ice3x2/kc2/docs/spec/20.kc2-no-stabilizer-layout.md

# KC2 No-Stabilizer Split Layout

| Field | Value |
|---|---|
| Document Type | layout_spec |
| Product | KC2 |
| Scope | Physical keyboard layout |
| Status | decided |
| Date | 2026-08-20 |
| Parent Spec | `../spec.md` |
| Related Research | `../research/kc2-plateless-low-profile-stabilizer-removal-2026-06-04.md` |

## 1. Purpose

This document defines the KC2 physical layouts for the plateless low-profile no-stabilizer direction. The verified `kc2-x3` baseline remains a 77-key layout, while the active `kc2-x3-v2` target uses the fixed 70-key v5 layout selected from 1:1 visual previews and subsequent left-thumb/modifier refinement.

Both variants split or replace every historical `>=2U` key so that no stabilizer is required. Duplicate legends such as `LShift`/`LShift`, `Enter`/`Enter`, and `Space`/`Space` are intentional physical-key decisions. Nonstandard keycaps may be 3D printed for the intended Choc V2 or MX assembly.

## 2. Policy

- Both no-stabilizer layouts use no `>=2U` physical keys, and `1.75U` is the largest permitted key width.
- The verified `kc2-x3` target retains its existing 77-key row extents and joined geometry.
- The active `kc2-x3-v2` target uses 70 keys and may reduce its PCB outline and joined geometry under `CON-ARCH-006`; the old `3.6 mm` inner-edge margin and fixed H1-H9 support pattern are not V2 invariants.
- V2 joined placement uses a `19.85 mm` one-unit seam pitch and a `1.80 mm` nominal gap between the actual selected keycap envelopes in both Choc V2 and MX assembly modes, within the tolerance defined by `CON-ARCH-006`. Rows 0-3 use `18.05 mm` / `18.05 mm` caps and `8.025 mm` center-to-PCB-edge offsets on both sides. The bottom `1.75U Space` / `1U B` seam uses `32.3375 mm` / `18.05 mm` caps, a `26.99375 mm` center pitch, and `15.16875 mm` / `8.025 mm` center-to-PCB-edge offsets. Every row retains a `3.80 mm` nominal joined PCB gap, and the complete joined Edge.Cuts polygons retain at least `1.00 mm` exact Euclidean clearance.
- Joined placement and reduced bezel shall not violate copper-to-edge, socket, pad, routing, manufacturing, controller, antenna, USB, reset, or battery-lead clearances.
- The verified historical `kc2-x3` compact controller keeps its `CON-ARCH-002` no-carrier-power contract: `J_PWR1` is absent and carrier battery power nets are absent. This rule does not apply to the active V2 target.
- The active `kc2-x3-v2` target follows `CON-ARCH-007`: each half has a direct-solder `J_BAT1`, local `BAT+`, `NN_B+`, and `GND`, and one `SW_PWR1` that interrupts BAT+ only. Battery negative remains directly connected to local GND. Pre-attached insulated battery leads are soldered to `J_BAT1`; detachable A2501/JST connectors, bare pouch-tab soldering, and a lower-housing battery-body cavity are prohibited. `BAT_LEAD_SLOT1` is a copper-free strain-relief feature identified by the exact board text `BAT STRAIN RELIEF`.
- V2 top-side service centers are exact: `J_BAT1` left `(115.8125, 59.4000)` R180 and right `(94.3000, 59.4000)` R0; `SW_PWR1` left `(115.8125, 63.4500)` R0 and right `(94.3000, 63.4500)` R180; `SW_RST1` left `(126.0625, 63.4500)` R0 and right `(84.0500, 63.4500)` R180. From each USB-facing outer edge toward the antenna, the order is POWER then RESET.
- Firmware may map duplicate physical legends to identical or separate behaviors; the physical layout intentionally does not force that choice.

## 3. KLE-Style JSON

### 3.1 Verified kc2-x3 77-key baseline

```json
{
  "left": [
    ["~", "1", "2", "3", "4", "5", "6"],
    [{ "w": 1.5 }, "TAB", "Q", "W", "E", "R", "T"],
    [{ "w": 1.75 }, "Caps", "A", "S", "D", "F", "G"],
    [{ "w": 1.25 }, "LShift", "LShift", "Z", "X", "C", "V", "B"],
    [{ "w": 1.25 }, "Ctrl", { "w": 1.25 }, "Win", { "w": 1.25 }, "Alt", { "w": 1.25 }, "Fn", "Space", { "w": 1.25 }, "Space"]
  ],
  "right": [
    [{ "x": 0.5 }, "7", "8", "9", "0", "-", "=", "BSPC", { "w": 1.25 }, "BSPC", "Del"],
    ["Y", "U", "I", "O", "P", "[", "]", { "w": 1.75 }, "\\", "Home"],
    [{ "x": 0.25 }, "H", "J", "K", "L", ";", "'", "Enter", { "w": 1.5 }, "Enter", "PgUp"],
    [{ "x": 0.75 }, "N", "M", ",", ".", "/", "RShift", "Fn", "Up", "PgDn"],
    [{ "x": 0.75 }, "B", "Space", "Space", "RAlt", "Fn", "RCtrl", "Left", "Down", "Right"]
  ]
}
```

### 3.2 Fixed kc2-x3-v2 70-key v5 layout

```json
{
  "left": [
    ["~", "1", "2", "3", "4", "5", "6"],
    [{ "w": 1.5 }, "TAB", "Q", "W", "E", "R", "T"],
    [{ "w": 1.75 }, "Caps", "A", "S", "D", "F", "G"],
    ["LShift", { "w": 1.25 }, "LShift", "Z", "X", "C", "V", "B"],
    [{ "w": 1.25 }, "Ctrl", { "w": 1.25 }, "Fn", { "w": 1.25 }, "Alt", { "w": 1.75 }, "Space", { "w": 1.75 }, "Space"]
  ],
  "right": [
    [{ "x": 0.5 }, "7", "8", "9", "0", "-", "=", { "w": 1.25 }, "BSPC", "Del"],
    ["Y", "U", "I", "O", "P", "[", "]", { "w": 1.75 }, "\\"],
    [{ "x": 0.25 }, "H", "J", "K", "L", ";", "'", { "w": 1.5 }, "Enter", "Enter"],
    [{ "x": 0.75 }, "N", "M", ",", ".", "/", "RShift", "Up", "Fn"],
    [{ "x": 0.75 }, "B", { "w": 1.75 }, "Space", { "w": 1.25 }, "RAlt", "RCtrl", "Left", "Down", "Right"]
  ]
}
```

## 4. Key Counts and Row Widths

| Variant | Half | Keys | Row widths including row offsets |
|---|---|---:|---|
| `kc2-x3` | Left | 32 | `7U`, `6.5U`, `6.75U`, `7.25U`, `7.25U` |
| `kc2-x3` | Right | 45 | `9.75U`, `9.75U`, `9.75U`, `9.75U`, `9.75U` |
| `kc2-x3` | Total | 77 | Verified baseline preserved |
| `kc2-x3-v2` | Left | 31 | `7U`, `6.5U`, `6.75U`, `7.25U`, `7.25U` |
| `kc2-x3-v2` | Right | 39 | `8.75U`, `8.75U`, `8.75U`, `8.75U`, `8.75U` |
| `kc2-x3-v2` | Total | 70 | Fixed v5 layout |

## 5. Split Decisions

| V2 area | Fixed v5 decision | Rationale |
|---|---|---|
| Left `Shift` | outer `1U LShift` + inner `1.25U LShift` | Places the wider Shift target on the inner/right position while remaining stabilizer-free. |
| Left bottom modifiers | `1.25U Ctrl`, `1.25U Fn` in the former Win position, `1.25U Alt` | Removes the former standalone 1U Fn switch and keeps a physical Fn on the left. |
| Left `Space` | `1.75U Space` + `1.75U Space` | Splits the removed Fn's 1U width evenly across the two Space keys without exceeding the no-stabilizer 1.75U limit. |
| Left Win behavior | simultaneous `Alt` + `Fn` -> `Win/LGUI` | Retains Win as a chord without a standalone physical Win switch. |
| Right top row | `1.25U BSPC` + `1U Del` | Replaces the former duplicate Backspace and removes the old outer Del column. |
| Right `Enter` | inner primary `1.5U Enter` + outer `1U Enter` | Matches the user's more comfortable Choc V1 experience. |
| Right shift row | `1U RShift` + `1U Up` + `1U Fn` | Moves Fn to the right of Up and removes PgDn. |
| Right bottom row | `1U B`, `1.75U Space`, `1.25U RAlt`, `1U RCtrl`, `1U Left`, `1U Down`, `1U Right` | Enlarges the main right Space without a stabilizer and fills the `8.75U` row. |
| Removed V2 keys | `Home`, `PgUp`, `PgDn`, one former right `Space`, and the former bottom-row right `Fn` position | Reduces the right half from 45 to 39 keys; Fn is retained beside Up. |

## 6. Implementation Notes

- The verified `kc2-x3` generator and firmware remain 77-key artifacts under `CON-ARCH-005`; they must not be silently converted to the V2 layout.
- The `kc2-x3-v2` generator, firmware transform, routing, housing, and fabrication manifests shall use the exact 70-key v5 map under `CON-ARCH-004`.
- Neither variant may create stabilizer markers, stabilizer footprints, or stabilizer keepouts.
- Right-side matrix column assignment must be regenerated and reviewed for the 39-key V2 half; naive row-array deletion is insufficient.
- The ZMK matrix and keymap should explicitly distinguish duplicate physical keys with stable physical IDs even when legends match.
- V2 joined visual and mechanical renders shall prove the keycap pitch and gap, concealed non-controller PCB outline, and the permitted controller/service exceptions defined by `CON-ARCH-006`.
- PCB regeneration, routing, firmware generation, housing generation, and DRC must be rerun after the V2 layout change. `CON-ARCH-004`, `CON-ARCH-006`, `CON-ARCH-007`, `REL-ARCH-001`, X-series preflight, fabrication-output inspection, deflection testing, and physical coupon/first-article evidence remain required before any orderable V2 claim.
- Historical `kc2-x3` regeneration must continue to prove `J_PWR1` and carrier battery nets are absent under `CON-ARCH-002`; these checks must not be applied to V2.
- Active `kc2-x3-v2` regeneration must instead prove the exact `CON-ARCH-007` `J_BAT1`/`SW_PWR1`/`SW_RST1` centers, BAT+ -> IMMS common -> ON throw -> `NN_B+`/U1 RAW continuity, direct B-/GND continuity, NC pad isolation, RST-to-GND behavior, strain relief, and component/copper/antenna/housing clearances.
