ice3x2/kc2/docs/reports/smooth-central-seam-20260914/wall-sections.png

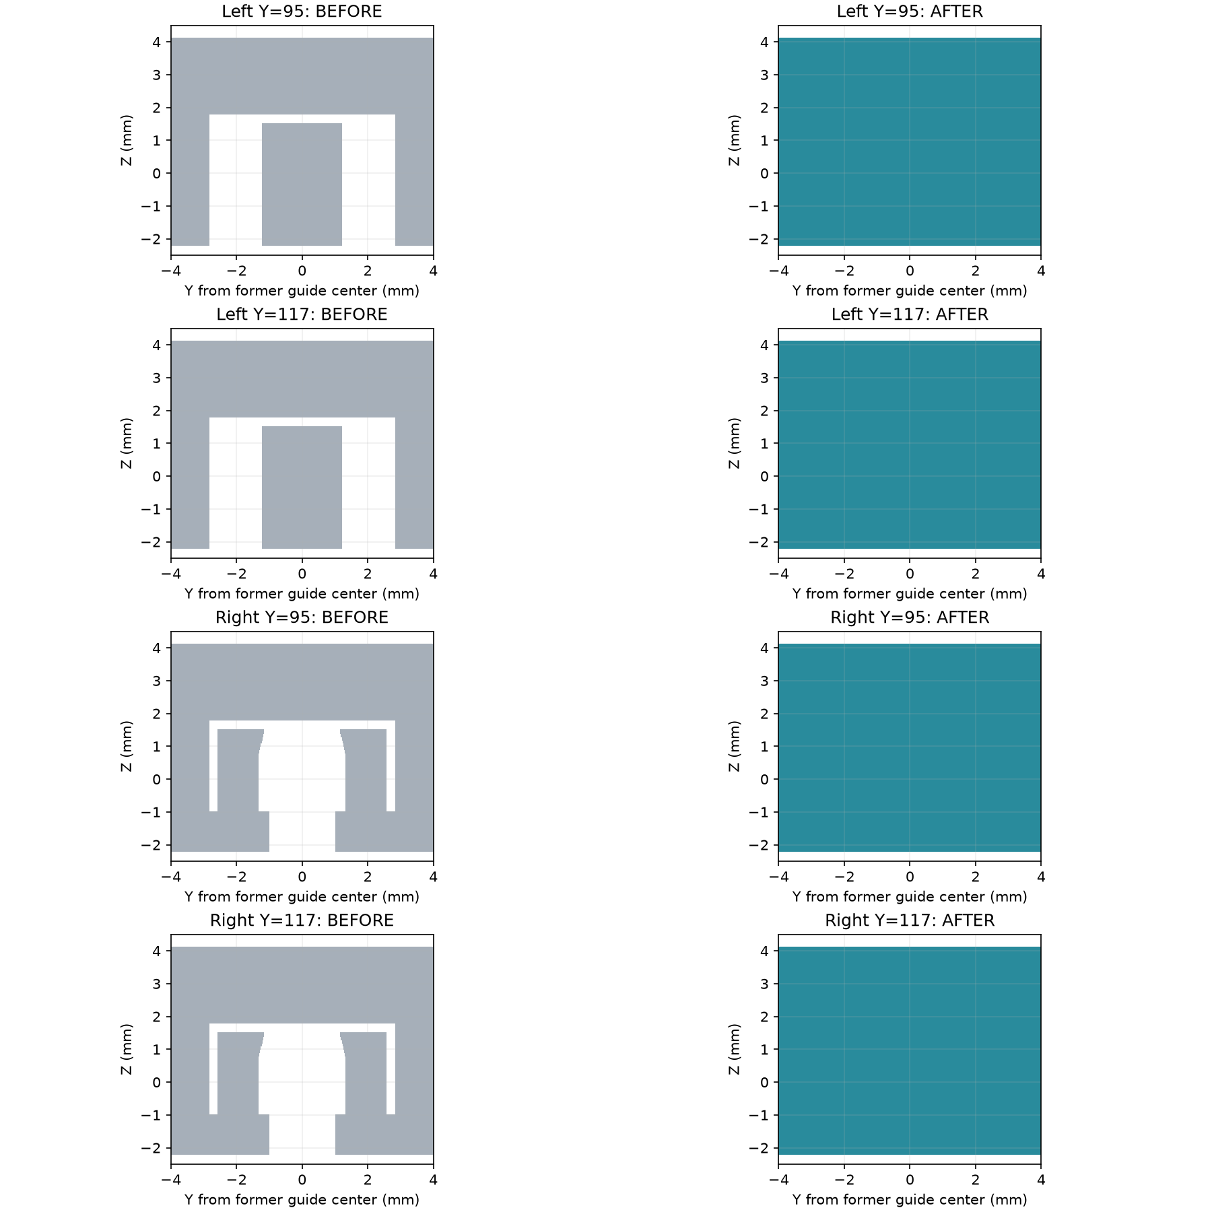
docs/reports/smooth-central-seam-20260914/wall-sections.png
