ice3x2/kc2/docs/reports/wrap-housings-20260920/left-sleeve-preview.png

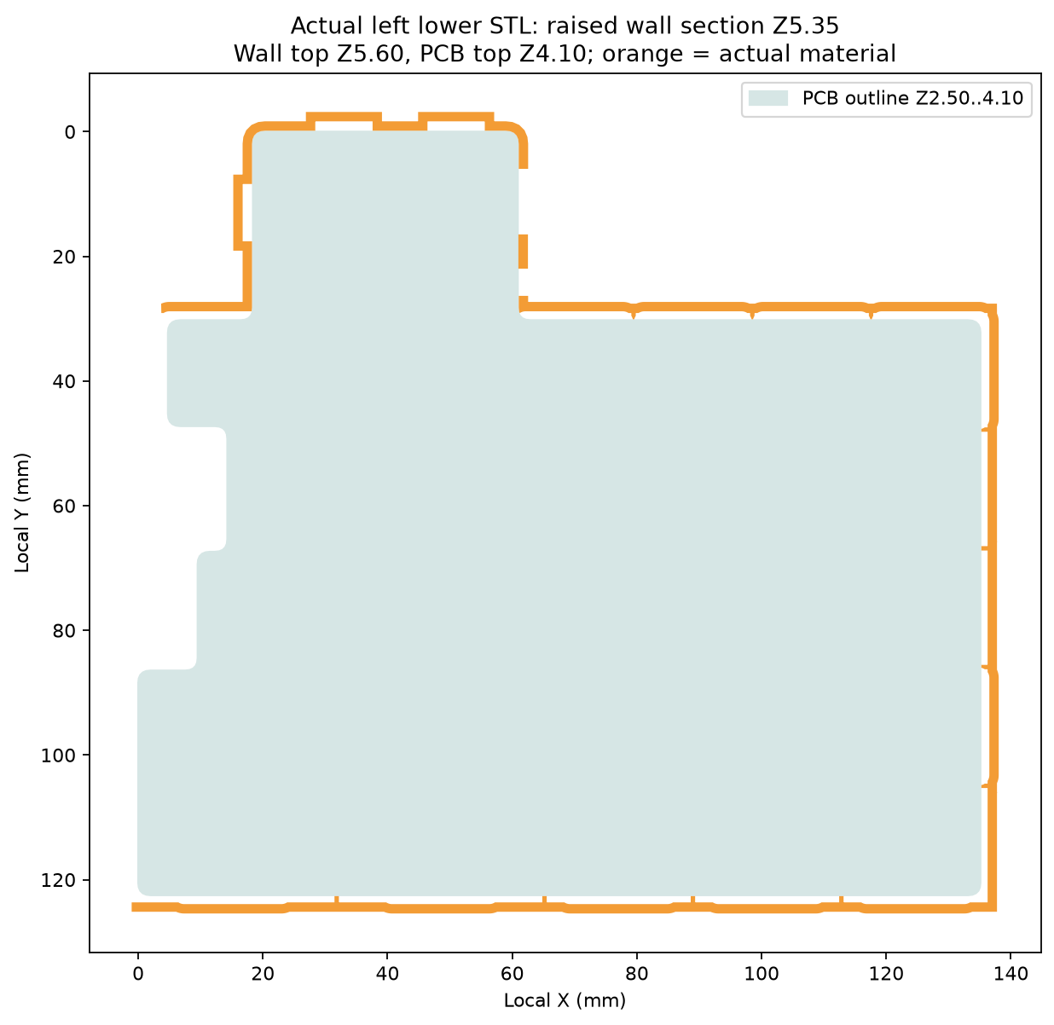
docs/reports/wrap-housings-20260920/left-sleeve-preview.png
