ice3x2/kc2/hardware/kicad/draft/hotswap/renders/kc2_left-hotswap_top.png

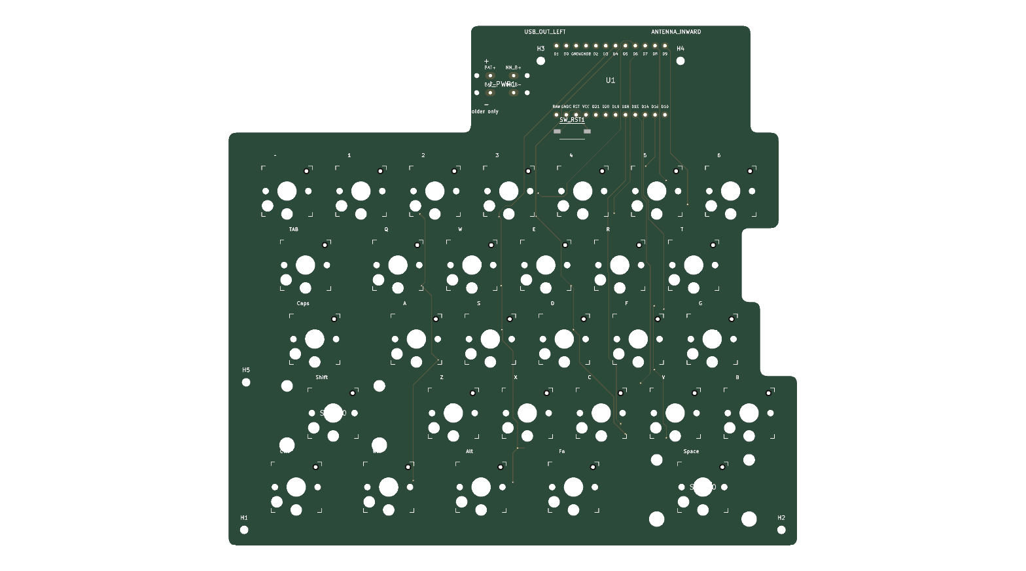
hardware/kicad/draft/hotswap/renders/kc2_left-hotswap_top.png
