ice3x2/kc2/hardware/kicad/fabrication_review/mx-visual-20260906/left-mechanical-1to1-preview.png

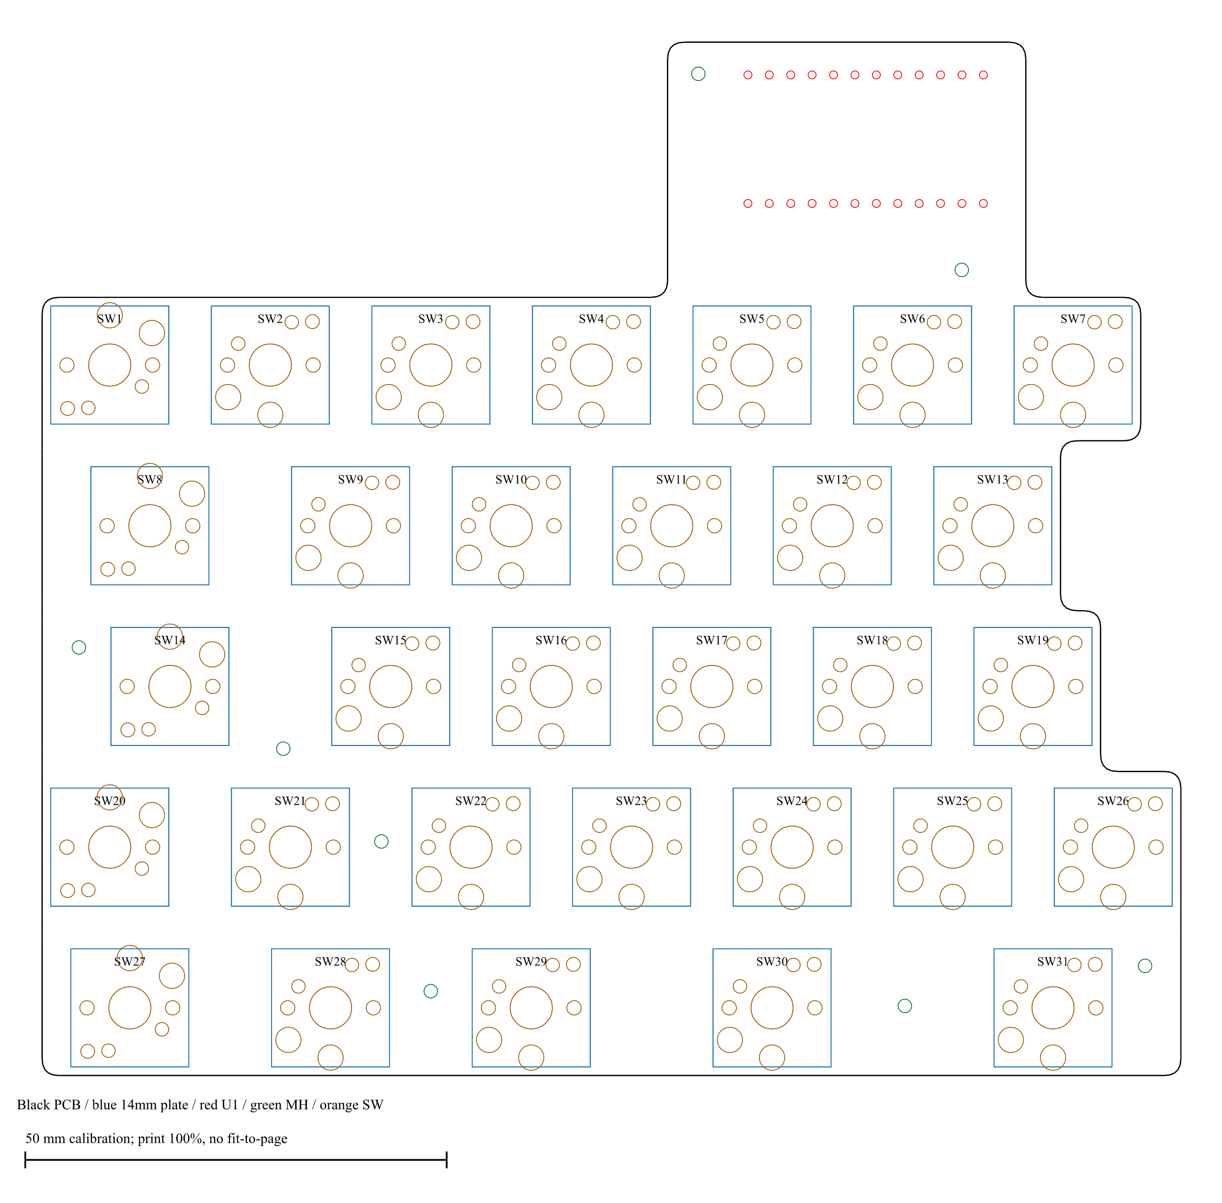
hardware/kicad/fabrication_review/mx-visual-20260906/left-mechanical-1to1-preview.png
