ice3x2/kc2/hardware/kicad/renders/kc2_join_seam_zoom.png

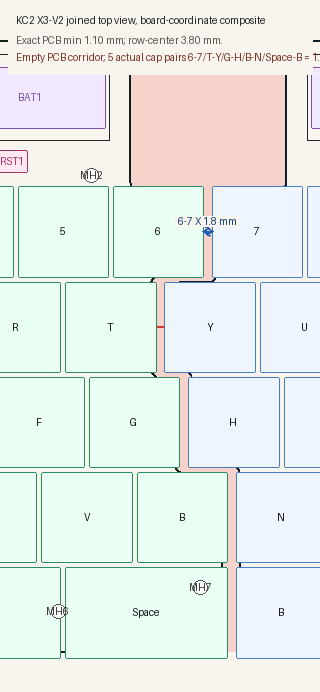
hardware/kicad/renders/kc2_join_seam_zoom.png
