ice3x2/kc2/hardware/kicad/renders/kc2_left_bottom.png

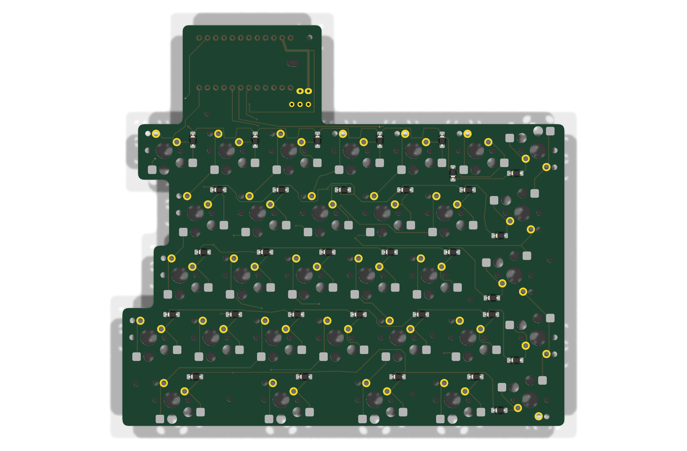
hardware/kicad/renders/kc2_left_bottom.png
