ice3x2/kc2/hardware/kicad/renders/kc2_right_bottom.png

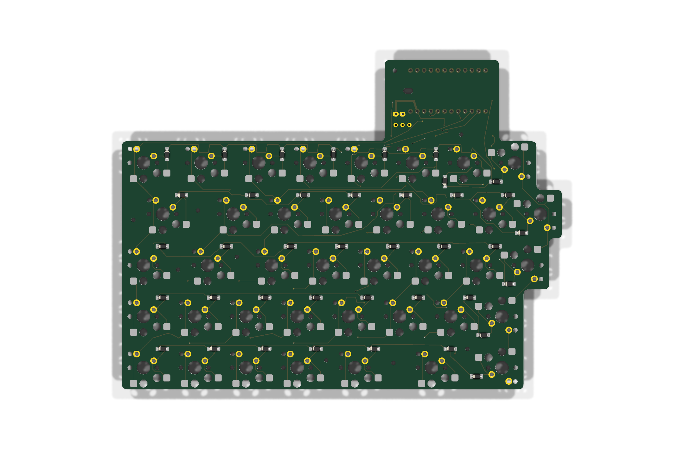
hardware/kicad/renders/kc2_right_bottom.png
