ice3x2/kc2/hardware/kicad/renders/kc2_right_top.png

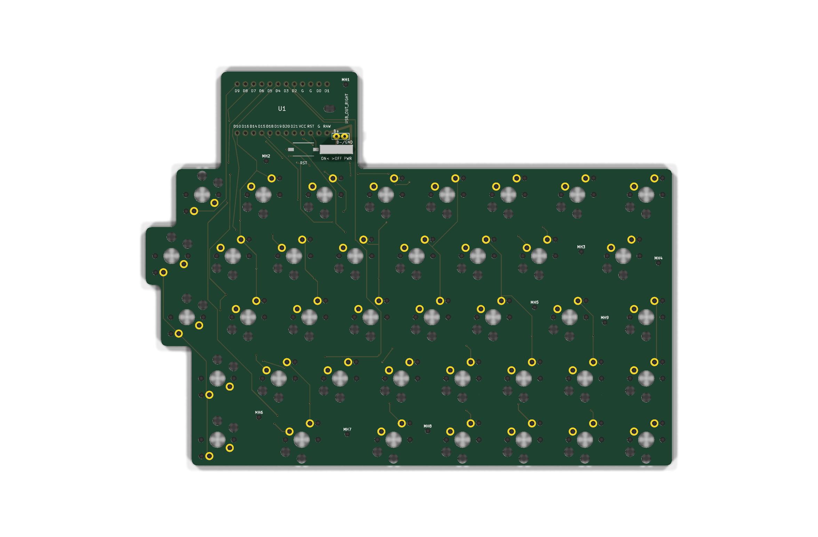
hardware/kicad/renders/kc2_right_top.png
