ice3x2/kc2/tmp_nw3/1322056_2.jpg

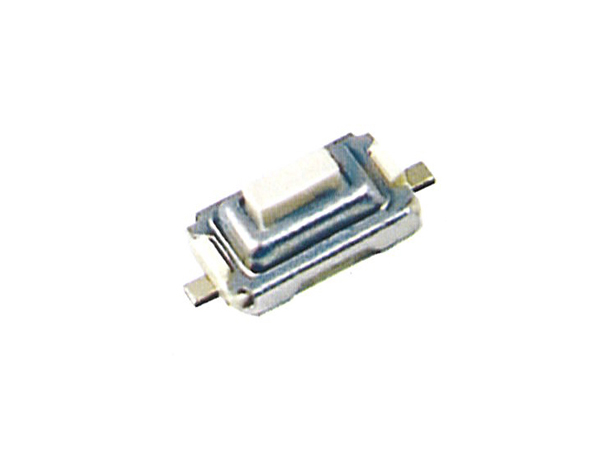
tmp_nw3/1322056_2.jpg
