ice3x2/kc2/hardware/kicad/fabrication/pcba_quote/kc2_left_jlcpcb_pcba_bom.csv

Comment | Designator | Footprint | LCSC Part #
Diodes Inc 1N4148W-13-F | D1,D2,D3,D4,D5,D6,D7,D8,D9,D10,D11,D12,D13,D14,D15,D16,D17,D18,D19,D20,D21,D22,D23,D24,D25,D26,D27,D28,D29,D30,D31 | SOD-123 | C112342
Kailh CPG135001S30 Choc hot-swap socket | SW1,SW2,SW3,SW4,SW5,SW6,SW7,SW8,SW9,SW10,SW11,SW12,SW13,SW14,SW15,SW16,SW17,SW18,SW19,SW20,SW21,SW22,SW23,SW24,SW25,SW26,SW27,SW28,SW29,SW30,SW31 | Kailh CPG135001S30 | C5333465
