ice3x2/kc2/hardware/MODELS/백업/kc2_right_lower_housing - 복사본.stl

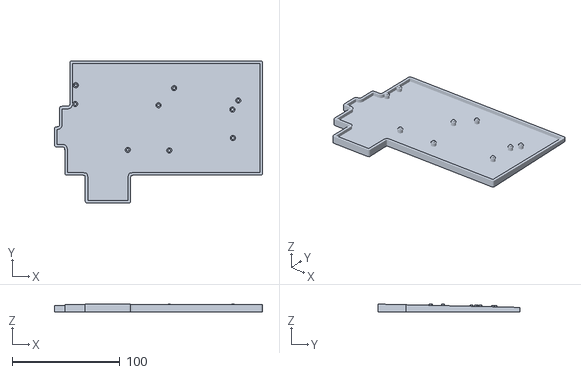
[picture p30: CAD file, 2026-06-15]
hardware/MODELS/백업/kc2_right_lower_housing - 복사본.stl
193.1 x 132.1 x 7.67
