ice3x2/kc2/docs/reports/reinforced-covers-20260913/native-check-left_lower_magnetic.step

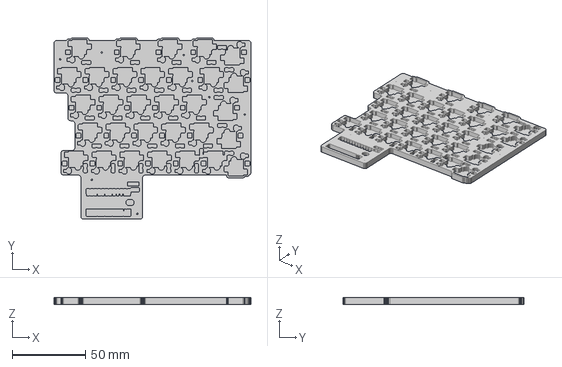
[picture p31: CAD file, 2026-09-12]
docs/reports/reinforced-covers-20260913/native-check-left_lower_magnetic.step
134.9 x 124.2 x 4.70 mm
