ice3x2/kc2/hardware/case/draft/x3-v2/kc2_right_x3_v2_lower_housing.step

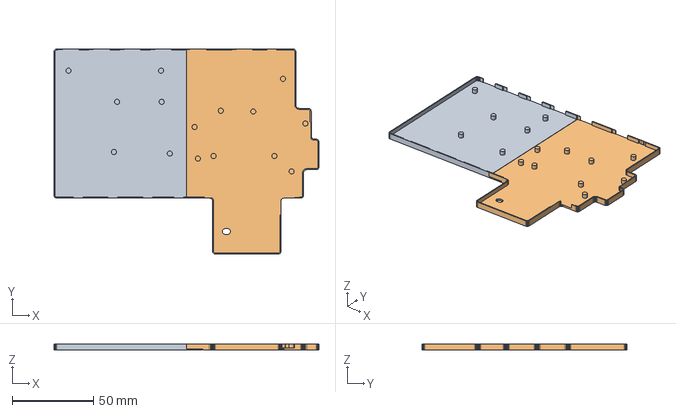
[picture p32: CAD file, 2026-08-20]
hardware/case/draft/x3-v2/kc2_right_x3_v2_lower_housing.step
163.5 x 126.6 x 3.90 mm
