ice3x2/kc2/hardware/case/kc2_right_lower_housing.step

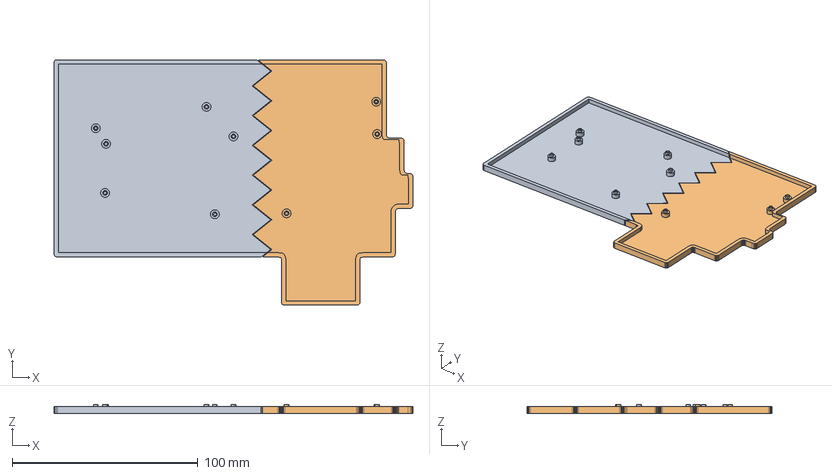
[picture p33: CAD file, 2026-08-03]
hardware/case/kc2_right_lower_housing.step
193.1 x 132.1 x 5.10 mm
