ice3x2/kc2/hardware/MODELS/adapters/kc2_mx_ring_cap_020.stl

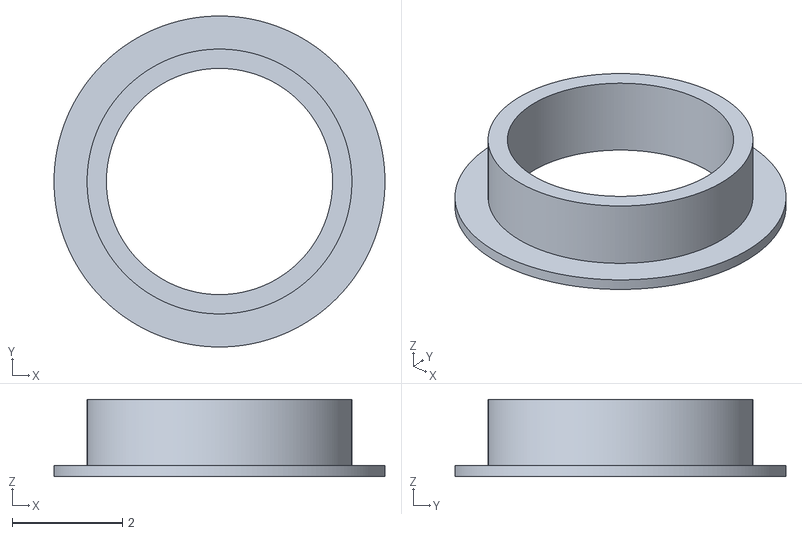
[picture p34: CAD file, 2026-09-06]
hardware/MODELS/adapters/kc2_mx_ring_cap_020.stl
6.00 x 6.00 x 1.40
