ice3x2/kc2/hardware/MODELS/kc2_right_lower_housing_part_b.stl

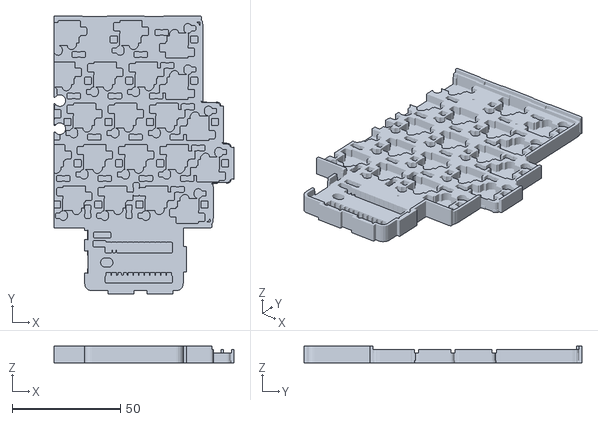
[picture p35: CAD file, 2026-09-21]
hardware/MODELS/kc2_right_lower_housing_part_b.stl
83.0 x 128.3 x 7.80
