ice3x2/kc2/hardware/MODELS/STL_FROM_FUSION_20260921/kc2_right_choc_v1_upper_housing_part_b.stl

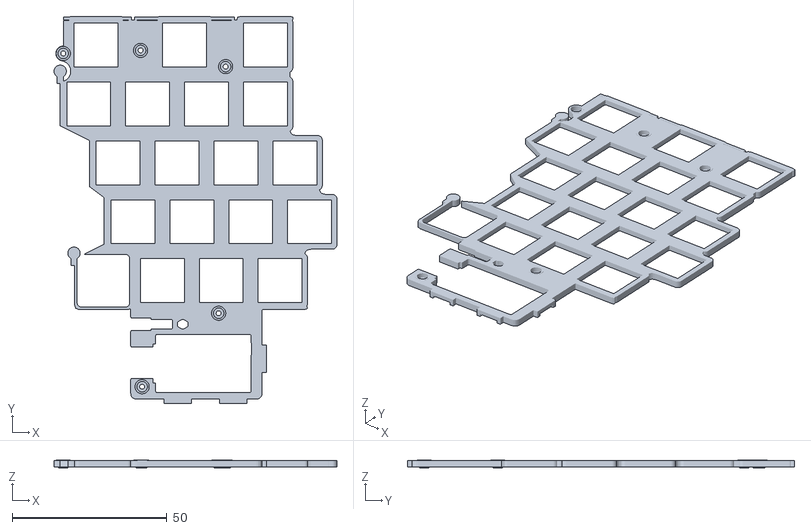
[picture p36: CAD file, 2026-09-21]
hardware/MODELS/STL_FROM_FUSION_20260921/kc2_right_choc_v1_upper_housing_part_b.stl
91.5 x 125.3 x 2.50
