ice3x2/kc2/hardware/MODELS/백업/kc2_left_lower_housing - 복사본.stl

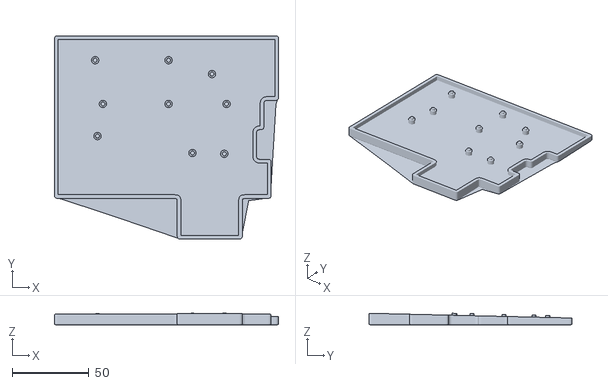
[picture p37: CAD file, 2026-06-15]
hardware/MODELS/백업/kc2_left_lower_housing - 복사본.stl
145.5 x 132.1 x 7.52
