ice3x2/kc2/docs/reports/registered-housing-fit-20260913/evidence/central/left-central-y95.step

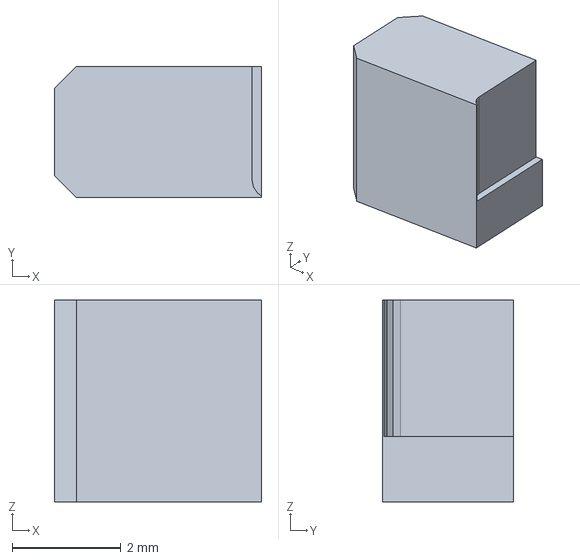
[picture p38: CAD file, 2026-09-14]
docs/reports/registered-housing-fit-20260913/evidence/central/left-central-y95.step
3.80 x 2.40 x 3.70 mm
