ice3x2/kc2/docs/reports/reinforced-covers-20260913/native-check-right_lower.step

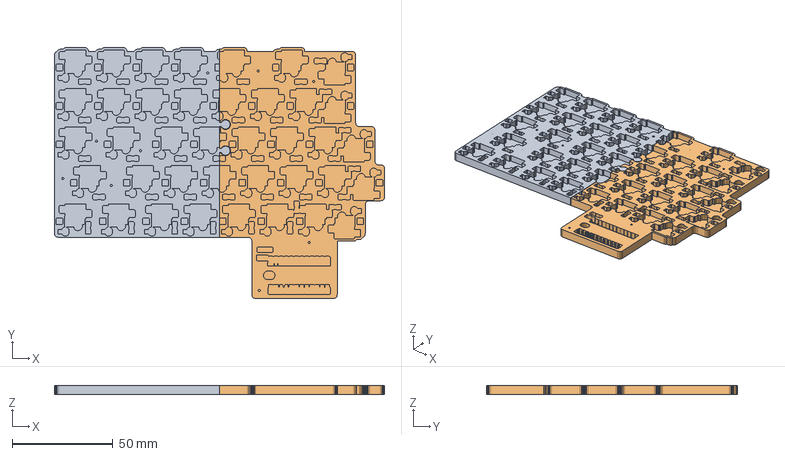
[picture p39: CAD file, 2026-09-12]
docs/reports/reinforced-covers-20260913/native-check-right_lower.step
163.5 x 124.2 x 4.70 mm
