ice3x2/kc2/hardware/MODELS/kc2_left_lower_housing.stl

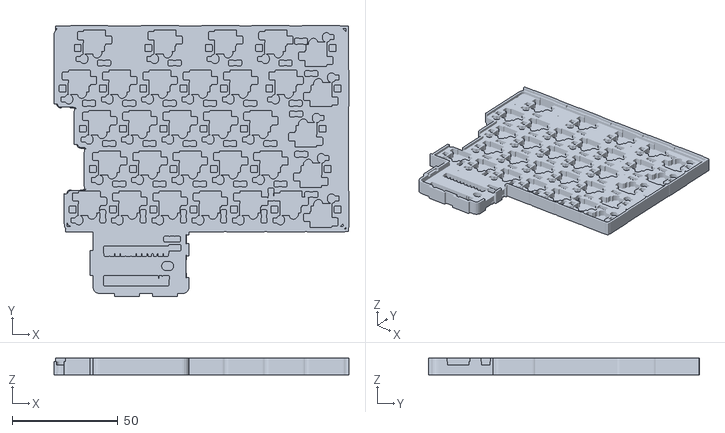
[picture p40: CAD file, 2026-09-21]
hardware/MODELS/kc2_left_lower_housing.stl
139.4 x 128.3 x 7.80
