ice3x2/kc2/hardware/MODELS/STL_FROM_FUSION_20260921/kc2_right_lower_housing_part_b_magnetic.stl

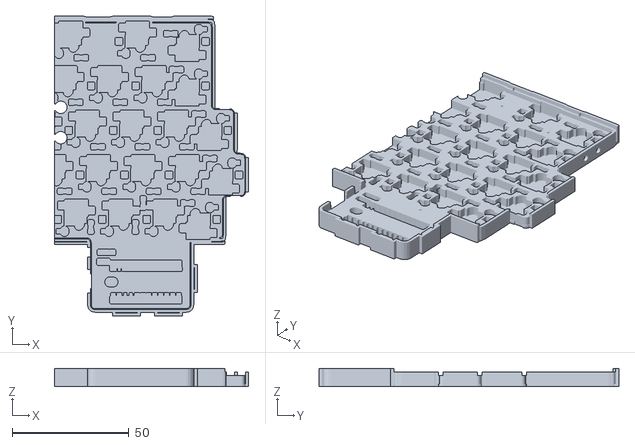
[picture p41: CAD file, 2026-09-21]
hardware/MODELS/STL_FROM_FUSION_20260921/kc2_right_lower_housing_part_b_magnetic.stl
83.0 x 128.3 x 7.80
