ice3x2/kc2/docs/reports/reinforced-covers-20260913/native-check-right_mx_upper.step

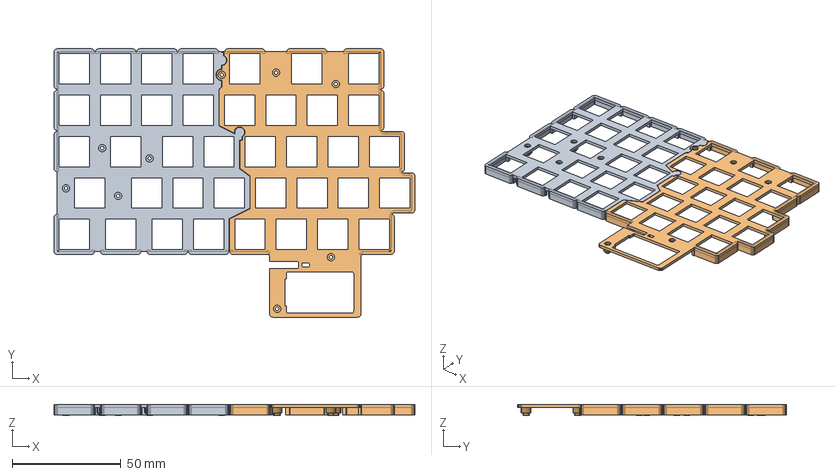
[picture p42: CAD file, 2026-09-12]
docs/reports/reinforced-covers-20260913/native-check-right_mx_upper.step
166.2 x 123.7 x 5.20 mm
