ice3x2/kc2/hardware/MODELS/kc2_right_deep_sea_upper_housing_part_a.stl

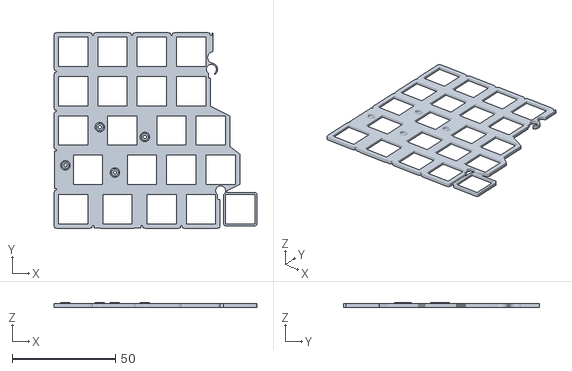
[picture p43: CAD file, 2026-09-21]
hardware/MODELS/kc2_right_deep_sea_upper_housing_part_a.stl
98.4 x 94.8 x 2.20
