ice3x2/kc2/hardware/MODELS/STL_FROM_FUSION_20260921/kc2_right_choc_v1_upper_housing_part_a.stl

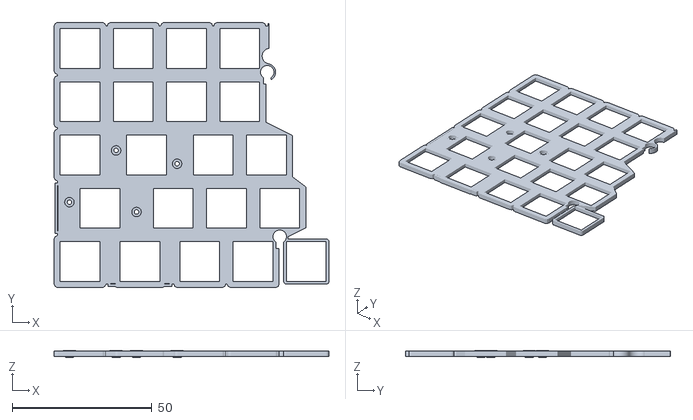
[picture p44: CAD file, 2026-09-21]
hardware/MODELS/STL_FROM_FUSION_20260921/kc2_right_choc_v1_upper_housing_part_a.stl
98.4 x 94.8 x 2.50
