ice3x2/kc2/hardware/MODELS/kc2_right_lower_housing_part_a.stl

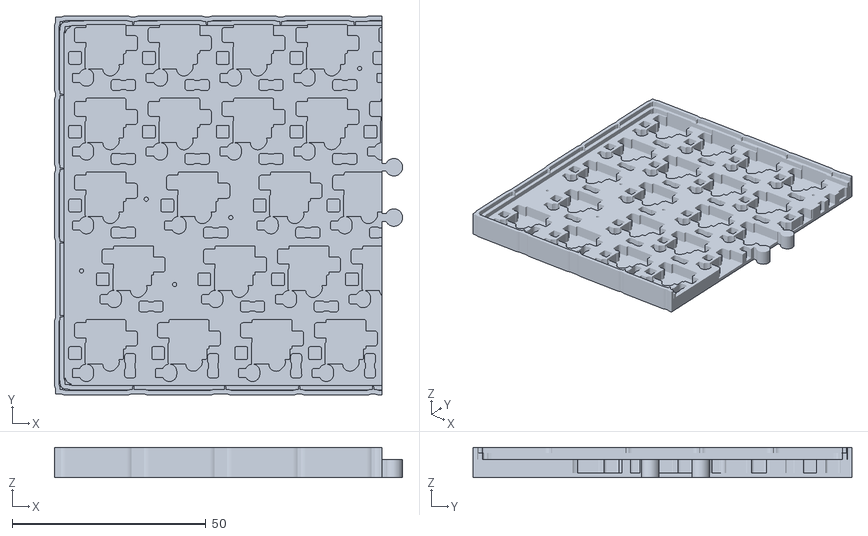
[picture p45: CAD file, 2026-09-21]
hardware/MODELS/kc2_right_lower_housing_part_a.stl
89.9 x 97.8 x 7.80
