ice3x2/kc2/hardware/MODELS/STL_FROM_FUSION_20260921/kc2_right_mx_upper_housing_part_b.stl

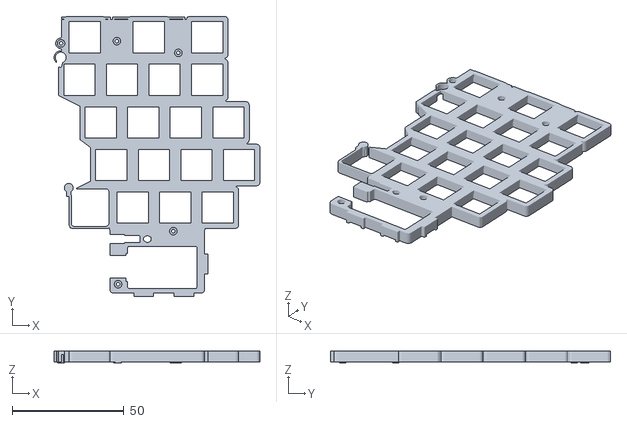
[picture p46: CAD file, 2026-09-21]
hardware/MODELS/STL_FROM_FUSION_20260921/kc2_right_mx_upper_housing_part_b.stl
92.1 x 125.3 x 5.20
