ice3x2/kc2/hardware/MODELS/kc2_right_deep_sea_upper_housing_part_b.stl

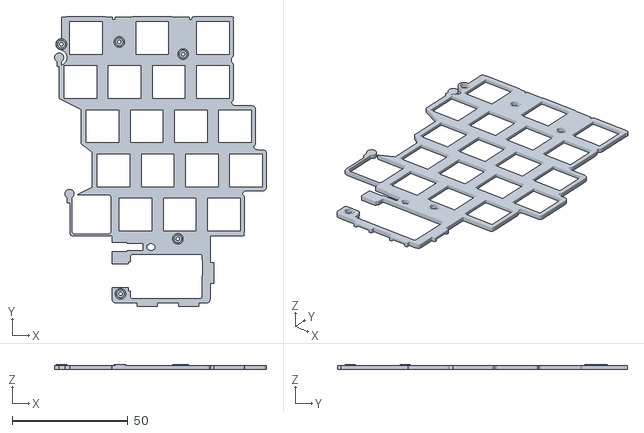
[picture p48: CAD file, 2026-09-21]
hardware/MODELS/kc2_right_deep_sea_upper_housing_part_b.stl
91.5 x 125.3 x 2.20
