ice3x2/kc2/hardware/MODELS/kc2_right_mx_upper_housing_part_a.stl

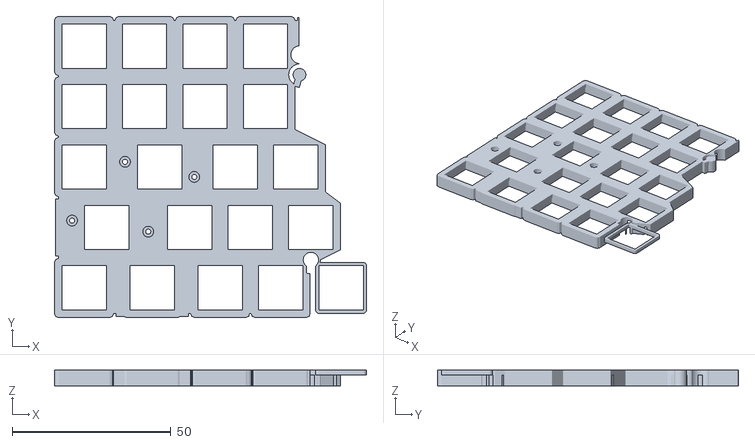
[picture p50: CAD file, 2026-09-21]
hardware/MODELS/kc2_right_mx_upper_housing_part_a.stl
98.3 x 94.8 x 4.90
