ice3x2/kc2/hardware/MODELS/STL_FROM_FUSION_20260921/kc2_right_lower_housing_part_a_magnetic.stl

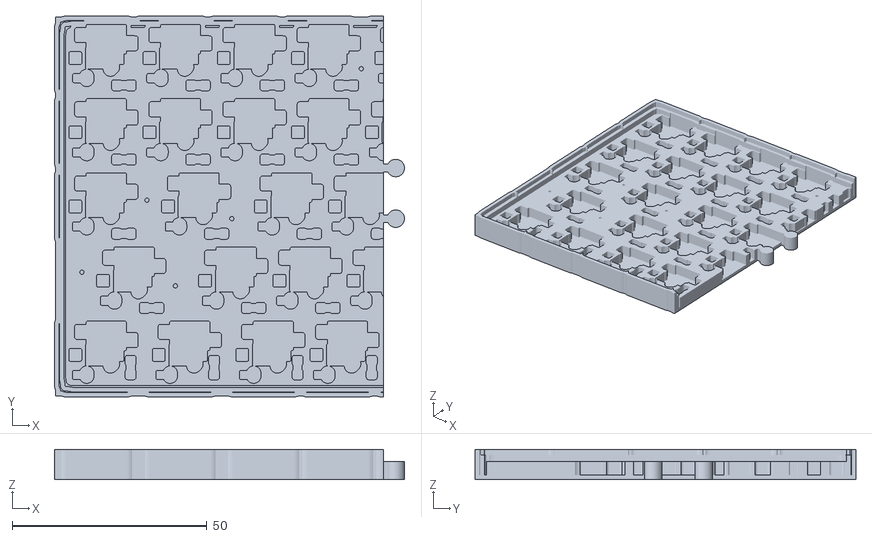
[picture p51: CAD file, 2026-09-21]
hardware/MODELS/STL_FROM_FUSION_20260921/kc2_right_lower_housing_part_a_magnetic.stl
89.9 x 97.8 x 7.80
