ice3x2/kc2/hardware/MODELS/kc2_left_deep_sea_upper_housing.stl

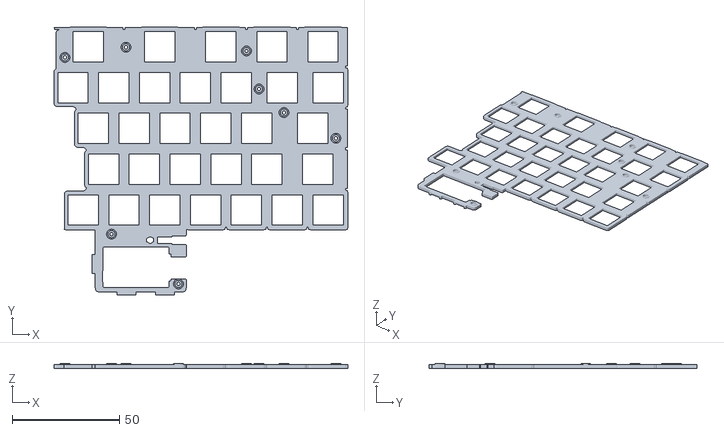
[picture p52: CAD file, 2026-09-21]
hardware/MODELS/kc2_left_deep_sea_upper_housing.stl
137.2 x 125.3 x 2.20
