ice3x2/kc2/hardware/MODELS/STL_FROM_FUSION_20260921/kc2_left_choc_v1_upper_housing.stl

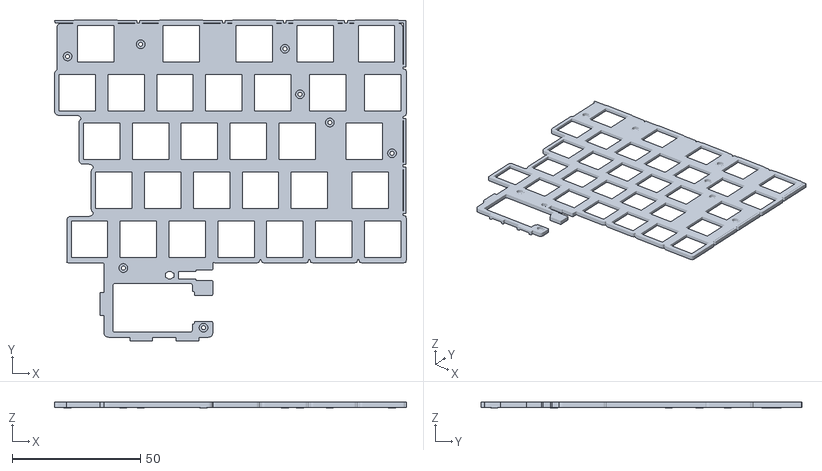
[picture p54: CAD file, 2026-09-21]
hardware/MODELS/STL_FROM_FUSION_20260921/kc2_left_choc_v1_upper_housing.stl
137.2 x 125.3 x 2.50
