ice3x2/kc2/hardware/MODELS/kc2_magnet_fit_coupon_magnetic.stl

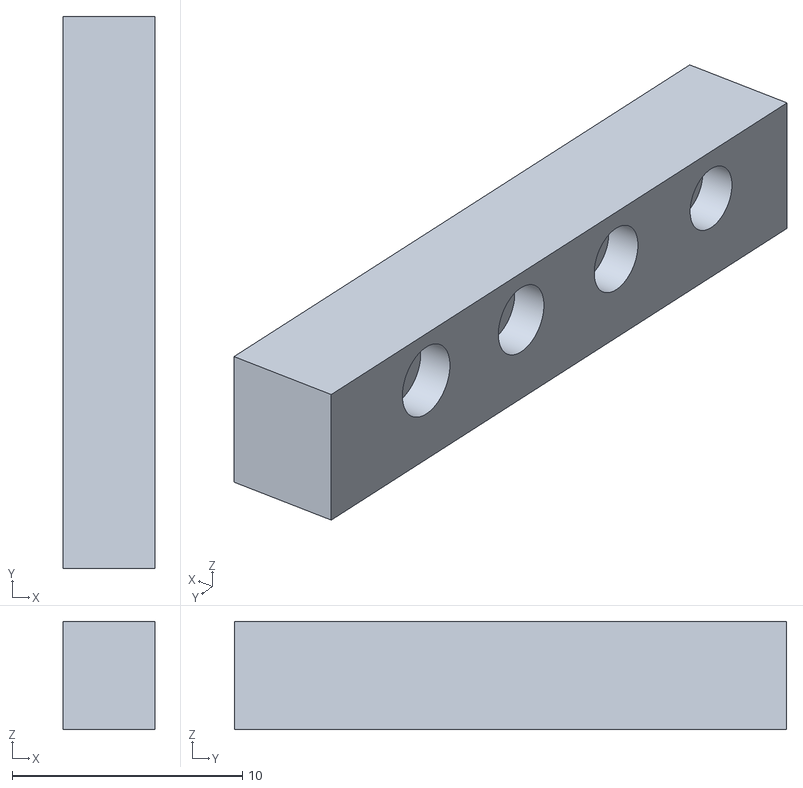
[picture p55: CAD file, 2026-09-07]
hardware/MODELS/kc2_magnet_fit_coupon_magnetic.stl
4.00 x 24.0 x 4.70
