ice3x2/kc2/hardware/MODELS/kc2_left_mx_upper_housing.step

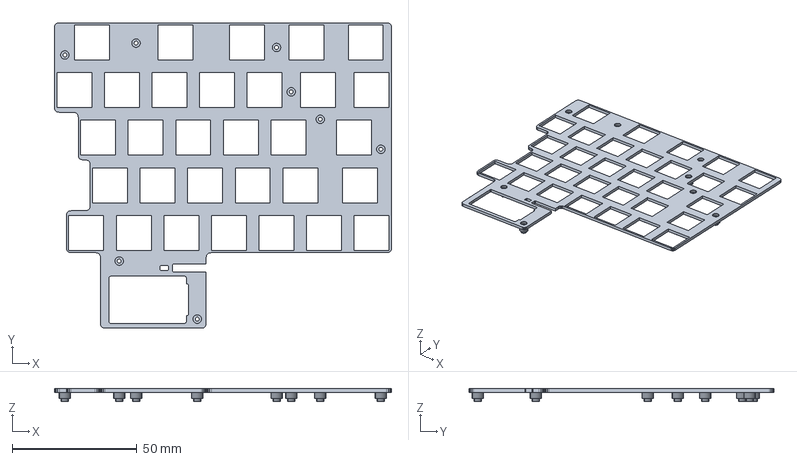
[picture p56: CAD file, 2026-09-07]
hardware/MODELS/kc2_left_mx_upper_housing.step
134.9 x 122.3 x 5.20 mm
