ice3x2/kc2/hardware/kicad/fabrication_review/mx-receptacle-20260906/README.md

# Inspection outputs — NOT APPROVED FOR ORDER

Requirements: CON-ARCH-004 AC-3/AC-8/AC-10, CON-ARCH-006, CON-ARCH-007.

This directory is for unzipped Gerber/Excellon inspection of the revised
canonical MX-receptacle PCB pair. It is not a fabrication release package.
No upload, purchase or assembly approval is given. Do not use historical
`hardware/kicad/fabrication/` ZIPs for this revised assembly.

Selected assembly: two individual open-bottom hat receptacles per switch,
with the printed MX plate-lid. Socket nominal length 3.00 mm, barrel OD 1.45 mm,
flange OD 2.00 mm, flange thickness 0.20 mm. MX finished-PTH design is a trial
1.60 mm; tolerance/contact fit is unqualified. U1 pads are 1.80 x 2.40 mm oval
with 0.95 mm drill; MX pads are 2.50 x 3.20 mm oval with 1.60 mm trial drill.

The generated copper/mask/drill files require source-geometry comparison and
visual inspection. Physical fit, exact MX switch, controller/service assembly,
housing fastener/printing qualification and power/RF testing remain open.
Do not infer readiness from file existence, DRC success or this directory name.
