ice3x2/kc2/docs/reports/registered-housing-fit-20260913/PRINT-draft.md

# 위치맞춤 외벽 하우징 — 게시 전 인쇄 안내 초안

이 문서는 보존된 이전 초안이며 현재 인쇄 지침이 아닙니다. [최종 인쇄 안내](../../../hardware/MODELS/PRINT-registered-housings.md)를 사용하세요.

요구사항: `CON-ARCH-006`, `CON-ARCH-007`, `OPS-ARCH-006`.
아직 최종 인쇄 승인이 아닙니다. 실제 검증과 canonical 게시 완료 후 사용할 안내 초안입니다.

## 부품 선택

상판은 MX, Choc V1, Deep Sea Mini 중 실제 스위치에 맞는 한 종류만 선택합니다. 각 종류의 왼쪽 STL 한 개와 오른쪽 `part_a`, `part_b` STL 각 한 개를 인쇄합니다. 하판은 무자석 또는 파일명에 `magnetic`이 있는 자석형 중 한 종류를 선택하여 같은 방식으로 세 개를 인쇄합니다. 총 상판 세 개와 하판 세 개입니다. 새 상판과 새 하판을 함께 사용하고 구형 부품을 섞지 마세요.

최종 게시 위치는 `hardware/MODELS`입니다. `.step`과 `.f3d`는 확인·편집용이며 오른쪽은 두 솔리드를 포함합니다. 150 mm 프린터에서는 반드시 분할 STL을 사용하세요. PCB와 이미 주문한 거버는 변경하지 않습니다.

`deep_sea`는 저상형 Deep Sea Mini 가족 도면 기준이며 일반 높이 Deep Sea Box용이 아닙니다. 구매 갈축 로트와 도면의 동일성은 아직 확인되지 않았습니다. Choc V1의 기존 0.20 mm 테두리 링 조건과 어댑터 안내는 유지합니다.

## 외벽과 조립

PCB는 종전처럼 하판 받침 위에 올립니다. PCB 바닥 Z2.50, 윗면 Z4.10이며, 외벽에 PCB를 압입하는 구조가 아닙니다. 기존 강화 소켓 가림벽을 유지합니다. 새 일반 외벽 상단은 Z4.10이고 넓은 상판 밑면 Z4.40과 명목 0.30 mm 여유가 있습니다.

각측 세 곳의 위치맞춤 돌기는 Z5.00까지 올라가며 상판의 외측 개방 홈에 들어갑니다. 홈 천장은 Z5.20, 안쪽면·양끝 여유는 한쪽 0.25 mm입니다. 돌기가 나사를 조이기 전 위치를 잡아주지만 나사 체결을 대신하지 않습니다. 중앙에는 위치맞춤 홈을 두지 않습니다. 공간이 부족한 중앙 세 구간에서는 새 상승벽만 국소 생략하고 기존 소켓 가림을 남깁니다.

오른쪽 A/B는 XY 방향으로 강제로 밀어 끼우지 말고 서로 맞물리는 위치에 높이를 달리해 놓은 뒤 Z 방향으로 내려 조립합니다. 명목 분할 여유는 약 0.40 mm입니다. 상판 맞물림은 머리 Ø4.00/목 2.00 mm, 하판은 머리 Ø4.50/목 2.00 mm입니다. 이는 좌우 키보드를 붙이는 중앙 결합부와 다른 구조·공차입니다.

좌우 전체 키보드는 중앙의 안내 혀 두 곳을 맞춰 수평으로 접근시킵니다. 중앙은 잠금 장치가 아니라 분리 가능한 국소 접촉 구조입니다. 끝부분의 명목 접촉량 0.02 mm는 실제 끼움 힘을 보증하는 값이 아닙니다. 출력 편차에 따라 헐겁거나 빡빡할 수 있으므로 힘으로 밀어 넣지 마세요.

## 출력과 물리 확인

- 단위 mm, 배율 100%. 전체 축척을 줄이면 스위치와 나사 위치가 PCB와 달라집니다.
- 하판은 평평한 바닥을 아래로 놓습니다. 새 중앙 탄성부의 빈 공간은 의도된 공간이므로 인필이나 접착제로 메우지 마세요.
- 오른쪽 중앙 두 곳에는 길이 5.70 mm의 국소 브리지가 있습니다. 해당 브리지와 탄성부 주변의 실제 슬라이서 경로를 확인해야 합니다. 지지 없이 반드시 인쇄된다는 보증은 아닙니다.
- 상판은 넓은 판 윗면을 아래로 놓는 방향을 검토합니다. V1 나사 보스는 판보다 0.10 mm, Deep Sea 보스는 0.35 mm 높아 뒤집었을 때 판 밑에 얕은 공중 시작 영역이 생깁니다. 빌드플레이트 연결 서포트 등으로 첫 층부터 지지되는지 확인하세요.
- 명목 1.20 mm 가림벽에 실제 연속 경로가 충분히 생성되는지 확인합니다. CAD가 솔리드여도 슬라이서는 인필을 만들 수 있으므로 내부까지 꽉 채운 출력물이 목적이라면 100% 인필을 사용하고 실제 경로를 별도로 확인하세요.
- 첫 층 눌림, 실뭉침, 브리지 처짐은 결합을 막을 수 있습니다. 중앙 끼움·A/B·위치맞춤 홈과 자석 입구를 먼저 시험 출력하여 확인하는 것이 좋습니다. 디지털 검증만으로 재료 강도·마찰·피로·흡착력은 확정할 수 없습니다.

## 나사와 자석

MX는 명목 M1.4×7.50 mm, 저상형은 M1.4×5.00 mm입니다. 길이는 머리 아래부터 측정합니다. MX 나사를 저상형에 사용하지 마세요. 통과 홀 Ø1.60 mm, 머리 포켓 Ø3.40 mm이며 설계 머리 범위는 최대 Ø3.00×높이 1.20 mm입니다. 나사 힘으로 들뜸이나 휨을 눌러 맞추지 마세요.

자석형은 Ø2×두께 1 mm 원통 자석용 기존 Ø2.40×깊이 1.20 mm 홈을 유지합니다. 새 외벽에 동축 Ø2.40 mm 삽입 통로를 추가하므로 바깥 입구에서 홈 뒷면까지는 2.80 mm입니다. 이 값은 자석을 받는 기존 홈 자체의 깊이와 다릅니다. 자석은 새 외벽의 통로를 지나 원래 안쪽 블라인드 홈에 안착시켜야 하며, 새 바깥 통로에 고정하지 마세요. 좌우 자석 극성을 먼저 확인하고 실제 끼움·접착·흡착력은 출력 후 확인하세요. 무자석형에는 삽입 통로가 없습니다.

실리콘 발의 배치와 접착 검토는 사용자 지시에 따라 이번 작업에서 보류했습니다.

조립 후 PCB 받침 접촉, 스위치 완전 안착·클립, 전원/리셋/USB 접근, 모든 키캡의 완전 눌림과 나사 머리 간섭을 직접 확인해야 합니다. 실제 납땜 돌출, 배선, 구매 부품 편차, 체결 토크 및 RF는 별도 물리 확인 대상입니다.
