ice3x2/kc2/docs/reports/wrap-housings-20260920/assembly-section-left-mx.png

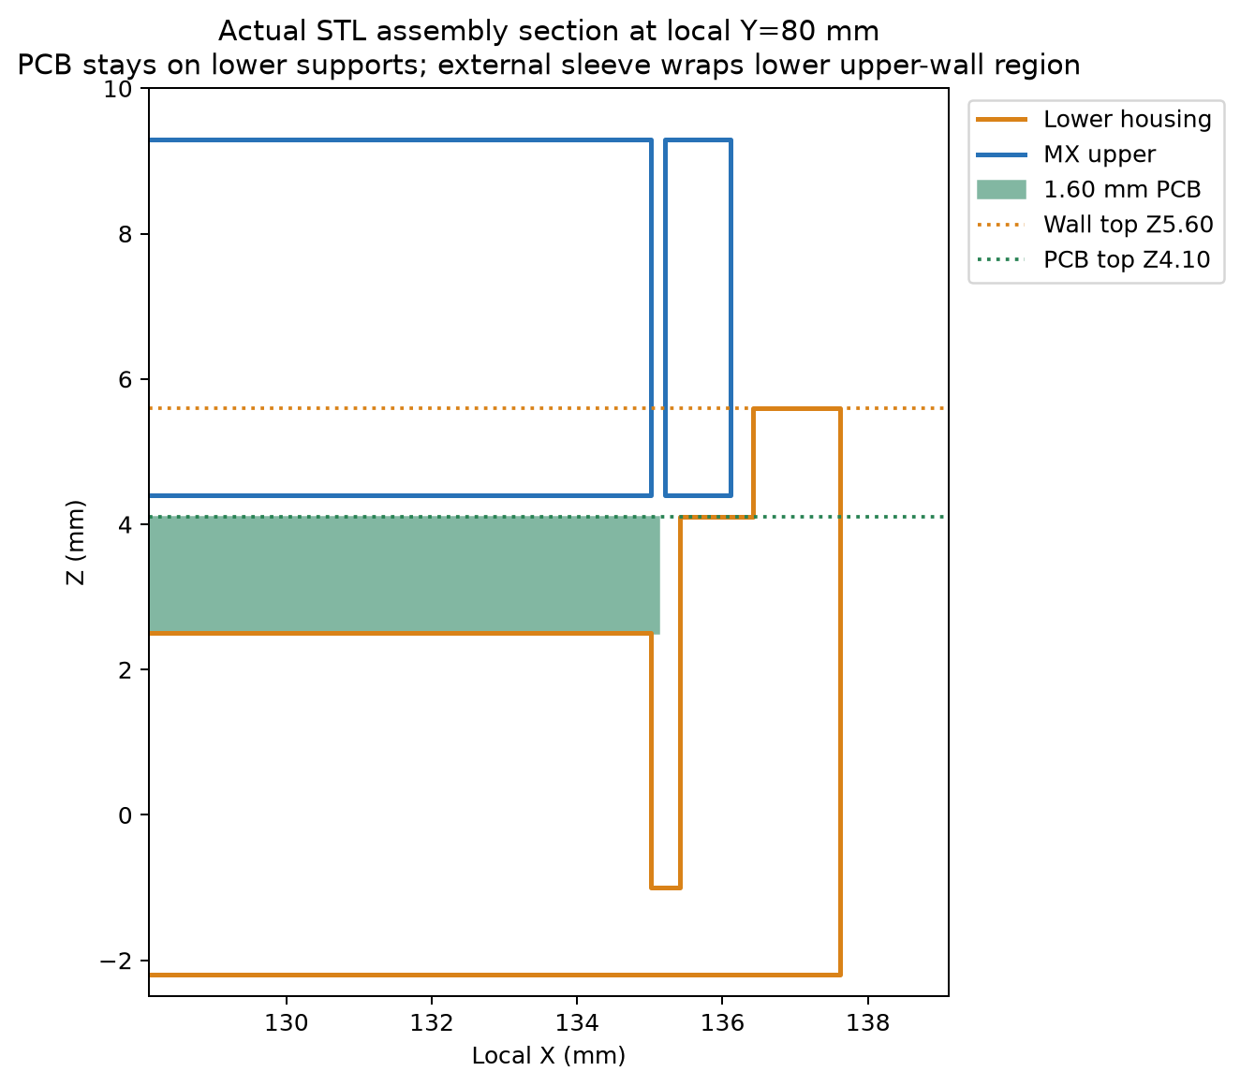
docs/reports/wrap-housings-20260920/assembly-section-left-mx.png
