ice3x2/kc2/hardware/kicad/draft/soldered/renders/kc2_left_top.png

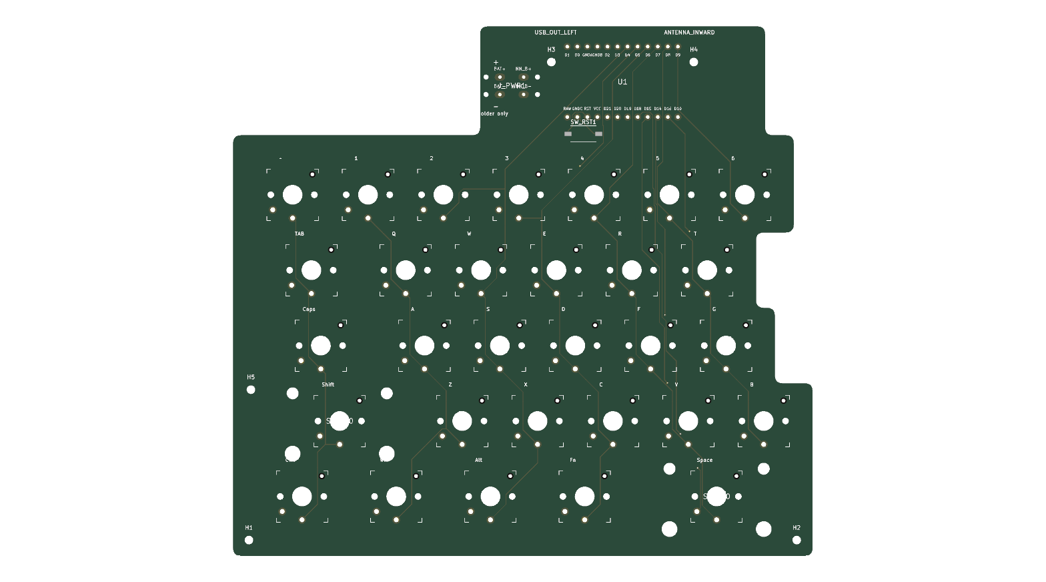
hardware/kicad/draft/soldered/renders/kc2_left_top.png
