ice3x2/kc2/hardware/kicad/fabrication_review/mx-visual-20260906/left-B_Cu-tile-0-0.png

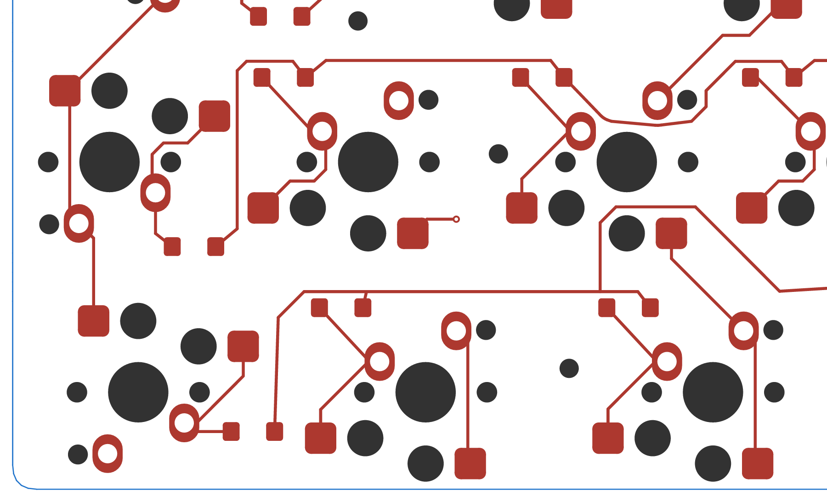
hardware/kicad/fabrication_review/mx-visual-20260906/left-B_Cu-tile-0-0.png
