ice3x2/kc2/hardware/kicad/fabrication_review/mx-visual-20260906/left-F_Mask-service.png

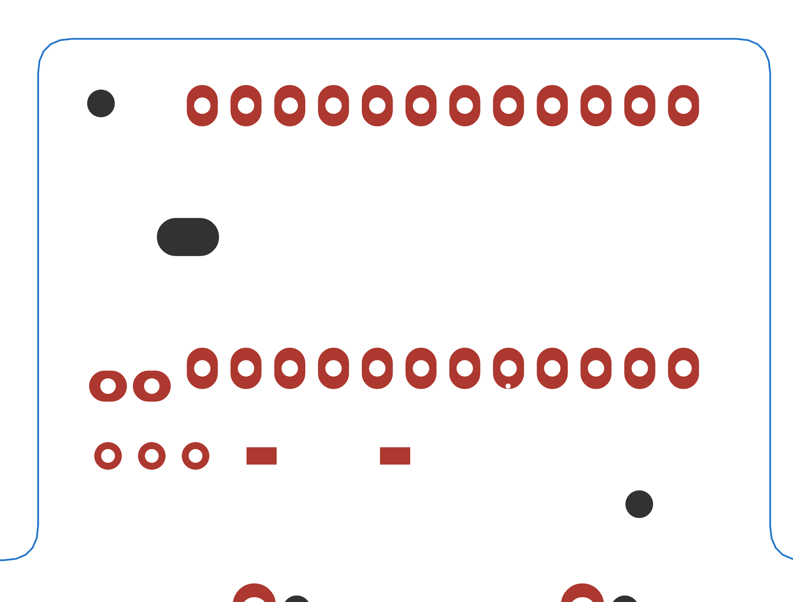
hardware/kicad/fabrication_review/mx-visual-20260906/left-F_Mask-service.png
