ice3x2/kc2/hardware/kicad/fabrication_review/mx-visual-20260906/right-B_Cu-tile-1-1.png

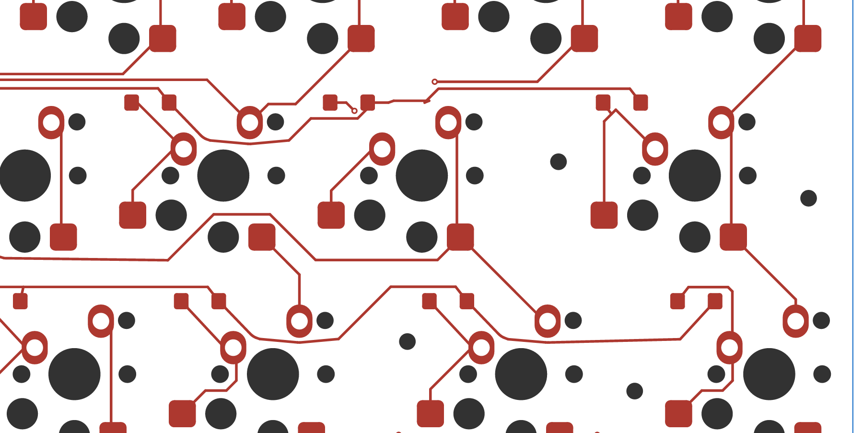
hardware/kicad/fabrication_review/mx-visual-20260906/right-B_Cu-tile-1-1.png
