ice3x2/kc2/hardware/kicad/fabrication_review/mx-visual-20260906/right-F_Silkscreen.png

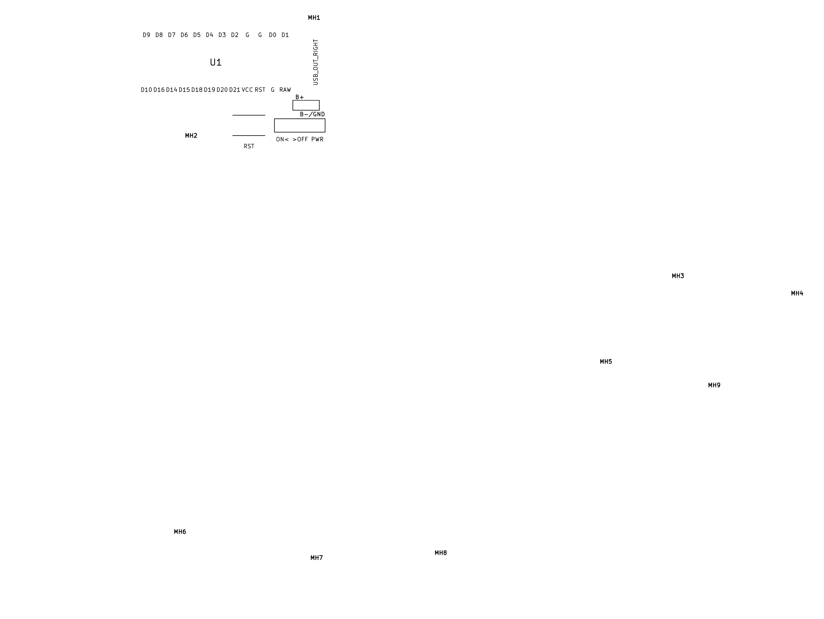
hardware/kicad/fabrication_review/mx-visual-20260906/right-F_Silkscreen.png
