ice3x2/kc2/hardware/kicad/fabrication_review/v1-recess-visual-20260906-r3/left-B_Cu-tile-1-1.png

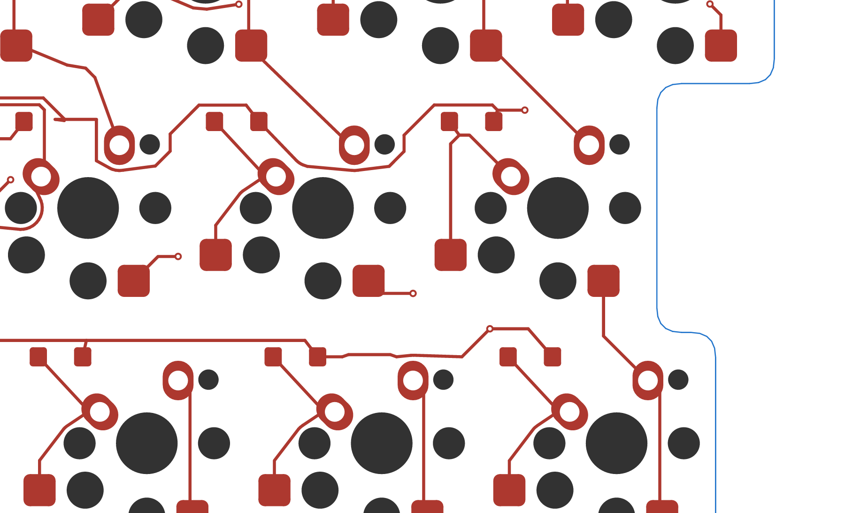
hardware/kicad/fabrication_review/v1-recess-visual-20260906-r3/left-B_Cu-tile-1-1.png
