ice3x2/kc2/hardware/kicad/fabrication_review/v1-recess-visual-20260906-r3/right-B_Cu-holes.png

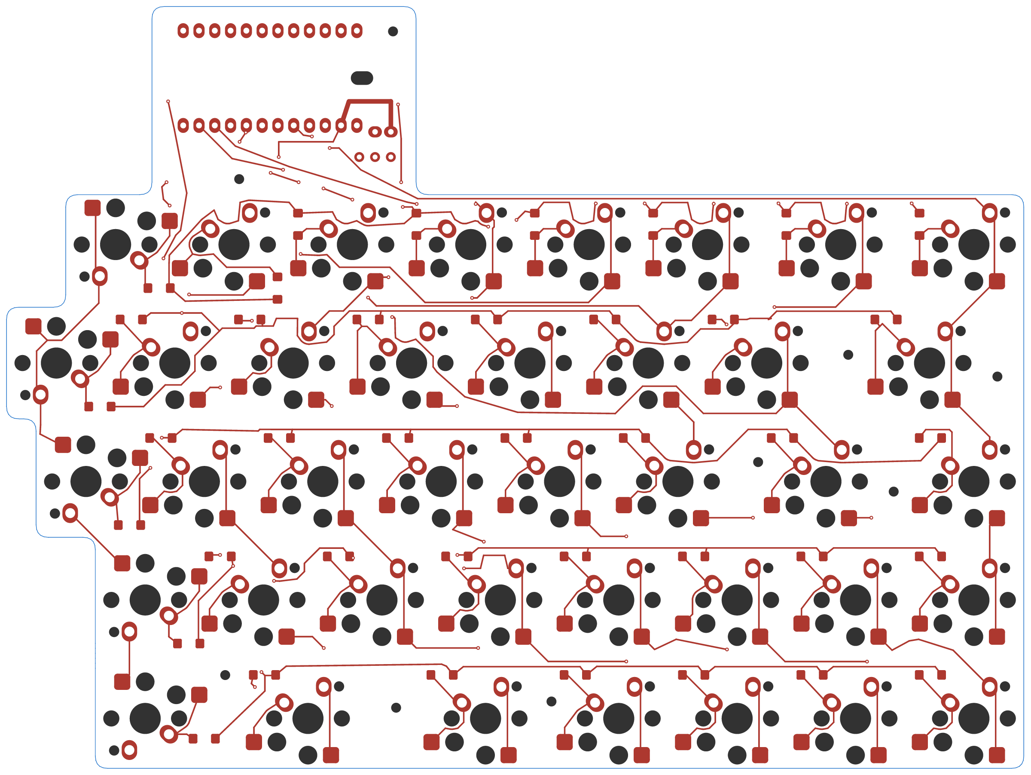
hardware/kicad/fabrication_review/v1-recess-visual-20260906-r3/right-B_Cu-holes.png
